psmitty7373/hotkey/default_images/draganddrop.png

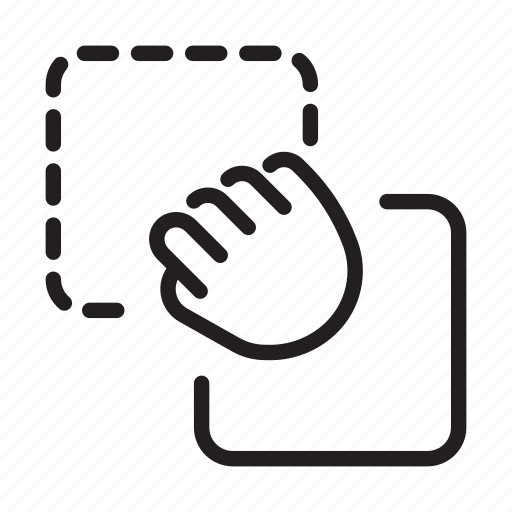
default_images/draganddrop.png
