psmitty7373/hotkey/default_images/trashcan.png

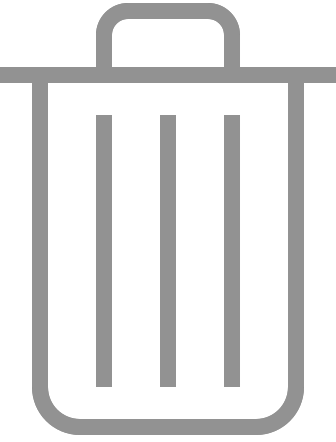
default_images/trashcan.png
