psmitty7373/hotkey/images/eagle_resupply.png

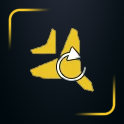
images/eagle_resupply.png
