psmitty7373/hotkey/images/hellbomb.png

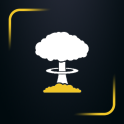
images/hellbomb.png
