psmitty7373/hotkey/images/orbital_380.png

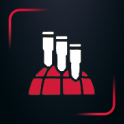
images/orbital_380.png
