psmitty7373/hotkey/images/orbital_gas.png

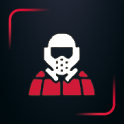
images/orbital_gas.png
