psmitty7373/hotkey/images/pack_jump.png

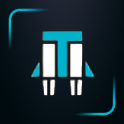
images/pack_jump.png
