psmitty7373/hotkey/images/support_arcthrower.png

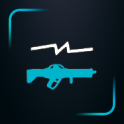
images/support_arcthrower.png
