psmitty7373/hotkey/images/support_autocannon.png

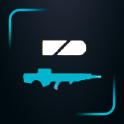
images/support_autocannon.png
