psmitty7373/hotkey/images/support_laser.png

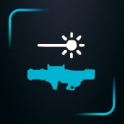
images/support_laser.png
