psmitty7373/hotkey/images/support_railgun.png

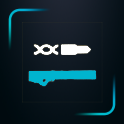
images/support_railgun.png
