psmitty7373/hotkey/images/support_spear.png

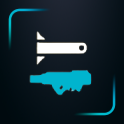
images/support_spear.png
