psmitty7373/hotkey/images/turret_manual.png

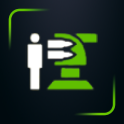
images/turret_manual.png
